jsoloPDX/Inductive-Proximity-MIDI-Controller-PSU-Capstone-Project-11/T11-firmware/calibration.c

//Code to calibrate Sensor 1
unsigned char AutoCalibrate_1(unsigned char StartingVoltage, unsigned int MinCalVal)
{
	// Turn on LED 1 & Power LED to indicate calibration for sensor 1 is in progress
	LED_ON_Power_One();

	// Set initial voltage. Delay long enough to reach steady state
	PWM_Change_PD5(StartingVoltage);
	_delay_ms(1000); 

	// Define current PWMValue
	unsigned char CurrentVoltage = StartingVoltage; 


	// Store ADC value for sensor
	unsigned int FrequencyToDCValue = 0; 
	FrequencyToDCValue = AnalogRead_MeanPC0(16);

	for (CurrentVoltage = StartingVoltage; CurrentVoltage <= 255; CurrentVoltage = CurrentVoltage + 1)
	{
		PWM_Change_PD5(CurrentVoltage); 
		_delay_ms(400); 
		FrequencyToDCValue = AnalogRead_MeanPC0(16);
		if (FrequencyToDCValue <= MinCalVal)
		{
			// Turn off LEDs
			LED_OFF_All();
			return(CurrentVoltage); 
		} 
	}
}



//Code to calibrate Sensor 2
unsigned char AutoCalibrate_2(unsigned char StartingVoltage, unsigned int MinCalVal)
{
	// Turn on LED 2 & Power LED to indicate calibration for sensor 1 is in progress
	LED_ON_Power_Two();

	// Set initial voltage. Delay long enough to reach steady state
	PWM_Change_PD6(StartingVoltage);
	_delay_ms(1000); 

	// Define current PWMValue
	unsigned char CurrentVoltage = StartingVoltage; 


	// Store ADC value for sensor
	unsigned int FrequencyToDCValue = 0; 
	FrequencyToDCValue = AnalogRead_MeanPC1(16);

	for (CurrentVoltage = StartingVoltage; CurrentVoltage <= 255; CurrentVoltage = CurrentVoltage + 1)
	{
		PWM_Change_PD6(CurrentVoltage); 
		_delay_ms(400); 
		FrequencyToDCValue = AnalogRead_MeanPC1(16);
		if (FrequencyToDCValue <= MinCalVal)
		{
			// Turn off LEDs
			LED_OFF_All();
			return(CurrentVoltage); 
		} 
	}
}


//Code to calibrate Sensor 3
unsigned char AutoCalibrate_3(unsigned char StartingVoltage, unsigned int MinCalVal)
{
	// Turn on LED 3 & Power LED to indicate calibration for sensor 1 is in progress
	LED_ON_Power_Three();

	// Set initial voltage. Delay long enough to reach steady state
	PWM_Change_PB3(StartingVoltage);
	_delay_ms(1000); 

	// Define current PWMValue
	unsigned char CurrentVoltage = StartingVoltage; 


	// Store ADC value for sensor
	unsigned int FrequencyToDCValue = 0; 
	FrequencyToDCValue = AnalogRead_MeanPC2(16);

	for (CurrentVoltage = StartingVoltage; CurrentVoltage <= 255; CurrentVoltage = CurrentVoltage + 1)
	{
		PWM_Change_PB3(CurrentVoltage); 
		_delay_ms(400); 
		FrequencyToDCValue = AnalogRead_MeanPC2(16);
		if (FrequencyToDCValue <= MinCalVal)
		{
			// Turn off LEDs
			LED_OFF_All();
			return(CurrentVoltage); 
		} 
	}
}
